ClaudeMarais/ShowerTimer_ESP32-C3-Mini/Images/RubberGasket.jpg

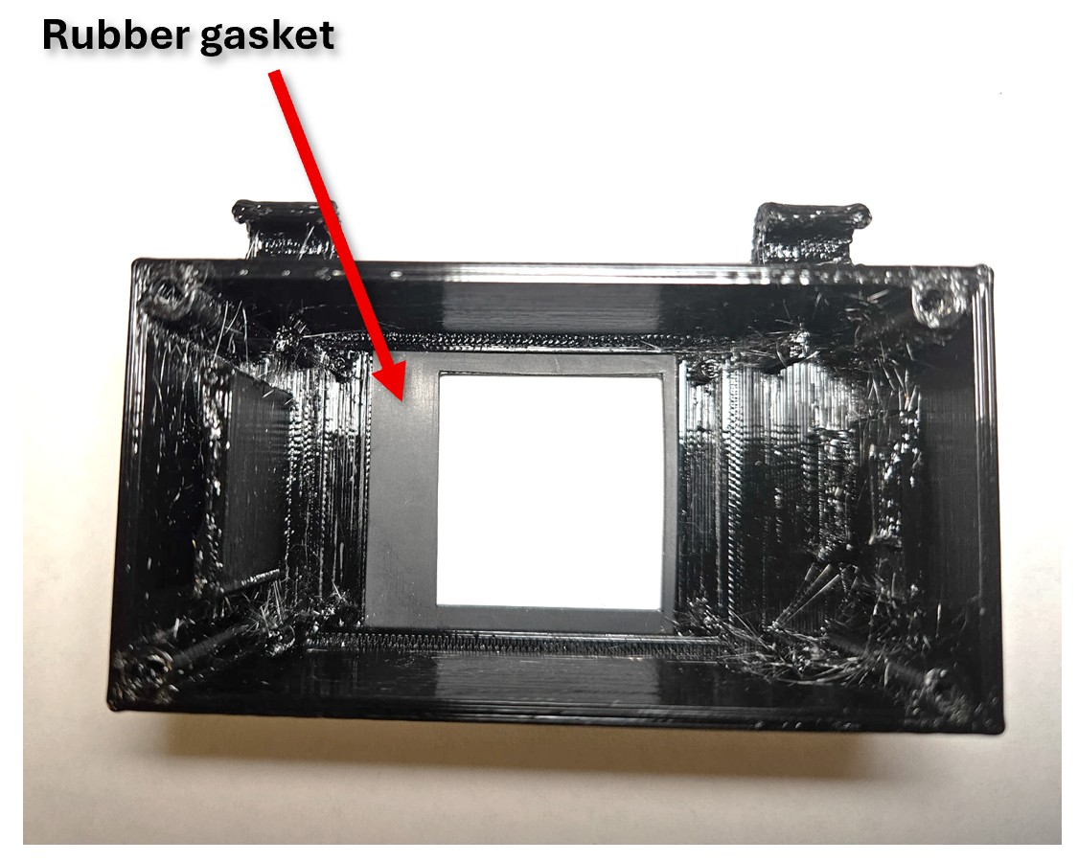
Images/RubberGasket.jpg
